jcybul/Carousel/Barrels/1.png

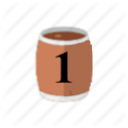
Barrels/1.png
