jcybul/Carousel/Barrels/10.png

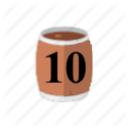
Barrels/10.png
